mensikv/VMs-macro-keyboard/images/VMs_macro_keyboard_wiring_1.jpg

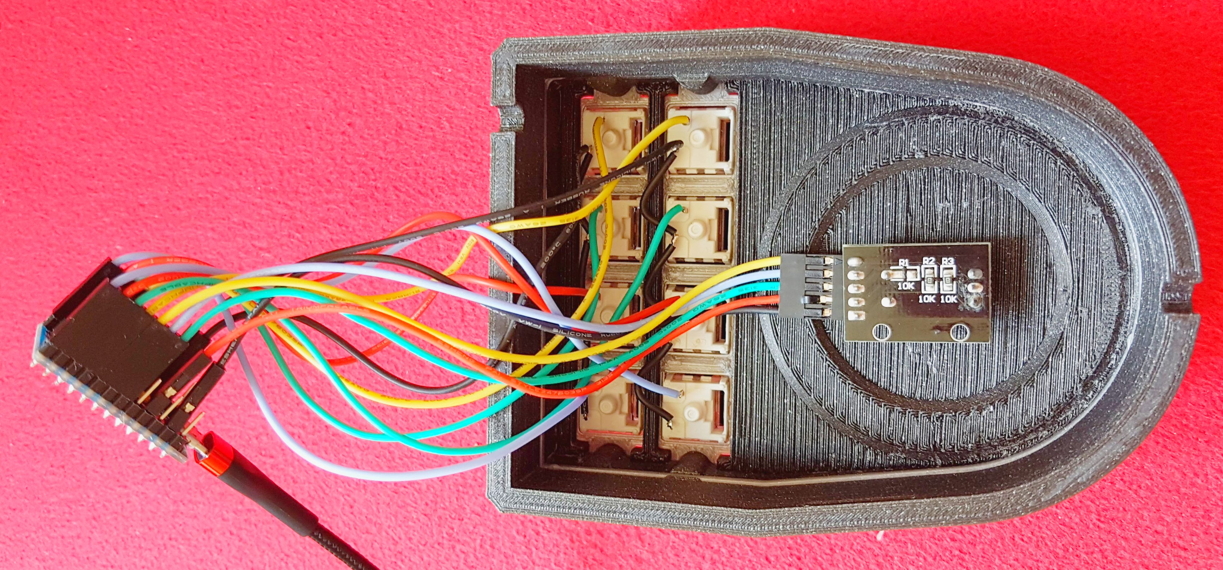
images/VMs_macro_keyboard_wiring_1.jpg
