mensikv/VMs-macro-keyboard/images/VMs_macro_keyboard_wiring_2.jpg

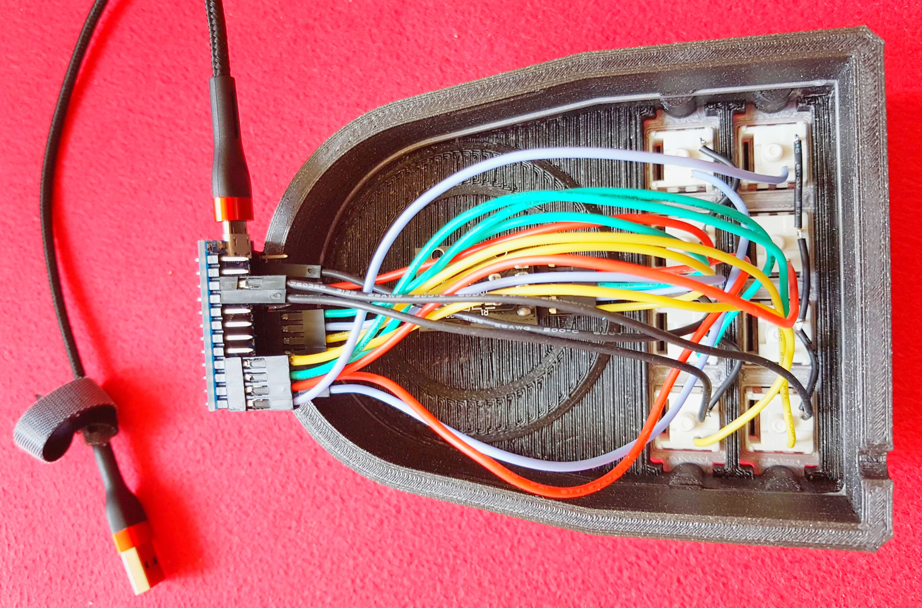
images/VMs_macro_keyboard_wiring_2.jpg
